tomarus/midirouter/verilator/top.cpp

#include "Vtop.h"
#include "verilated.h"
#include "verilated_vcd_c.h"
// #include "Vtop__Dpi.h"
#include "svdpi.h"

#include <iostream>
using namespace std;

// 0xfc
int serialOut[10] = {0, 0, 0, 0, 0, 0, 0, 1, 1, 1};

int main(int argc, char **argv, char **env) {
	int i;
	int clk;
	Verilated::commandArgs(argc, argv);
	// init top verilog instance
	Vtop *top = new Vtop;
	Verilated::scopesDump();
	svScope x = svSetScope(svGetScopeFromName("TOP.top"));
	cout << x << endl;

	// cout << svGetScope() << endl;

	// init trace dump
	Verilated::traceEverOn(true);
	VerilatedVcdC *tfp = new VerilatedVcdC;
	top->trace(tfp, 99);
	tfp->open("trace.vcd");

	// initialize simulation inputs
	top->clk = 1;
	top->rst = 1;
	top->inport = -1;

	// run simulation for X clock periods
	for (i = 0; i < 100000; i++) {
		top->rst = (i < 2);
		tfp->dump(i);
		top->clk = !top->clk;
		top->eval();
		if (Verilated::gotFinish()) {
			break;
		}

		if (i%2==1) {
			clearbyte(0);
			clearbyte(1);
		}

		switch(i) {
			// case 12:
			// 	// first test byte
			//     sendbyte(0, 0xf8, 0);
			//     break;
			case 10:
				// send note off sequence sourceport 0 destport 0
				sendbyte(0, 0x90, 0); // 0x90 0x55 0x33
				break;
			case 14:
				// send note on sequence sourceport 1 destport 0
				// this should be merged after note off sequence
				sendbyte(0, 0x80, 1); // 0x80 0x44 0x22
				break;
			case 20:
				sendbyte(0, 0x55, 0);
				break;
			case 24:
				sendbyte(0, 0x44, 1);
				break;
			case 28:
				sendbyte(0, 0x33, 0);
				break;
			case 125:
				// should be merged with priority
				sendbyte(0, 0xf8, 0);
				break;
			case 255:
				// should be merged with priority
				sendbyte(0, 0xf8, 0);
				break;
			case 260: // XXX: hehe
				sendbyte(0, 0x22, 1);
				break;
			case 500:
				sendbyte(0, 0xb3, 5); // 0xb3 0x11 0x12
				break;
			case 504:
				sendbyte(0, 0xb9, 3); // 0xb3 0x11 0x12
				break;
			case 508:
				sendbyte(0, 0x11, 3);
				break;
			case 512:
				sendbyte(0, 0x11, 5);
				break;
			case 516:
				sendbyte(0, 0x12, 3);
				break;
			case 520:
				sendbyte(0, 0x12, 5);
				break;
			case 524:
				sendbyte(0, 0x15, 5);
				break;
			case 528:
				sendbyte(0, 0x15, 5);
				break;
			case 532:
				sendbyte(0, 0x13, 3);
				break;
			case 536:
				sendbyte(0, 0xf8, 3);
				break;
			case 540:
				sendbyte(0, 0x13, 3);
				break;
			case 700:
				// should be merged with priority
				sendbyte(0, 0xf8, 0);
				break;
		}

		if (i>=600 && i<=620 && i&1==1) {
			int x = serialOut[(i - 600) / 2];
			x |= 0xfffffffe;
			top->inport = x;
		}
	}
	tfp->close();
	exit(0);
}
